FrancisUsher/fauxrmie/40s-2040rmie.kicad_sch

## KiCad design 40s-2040rmie.kicad_sch (2023-11-17)

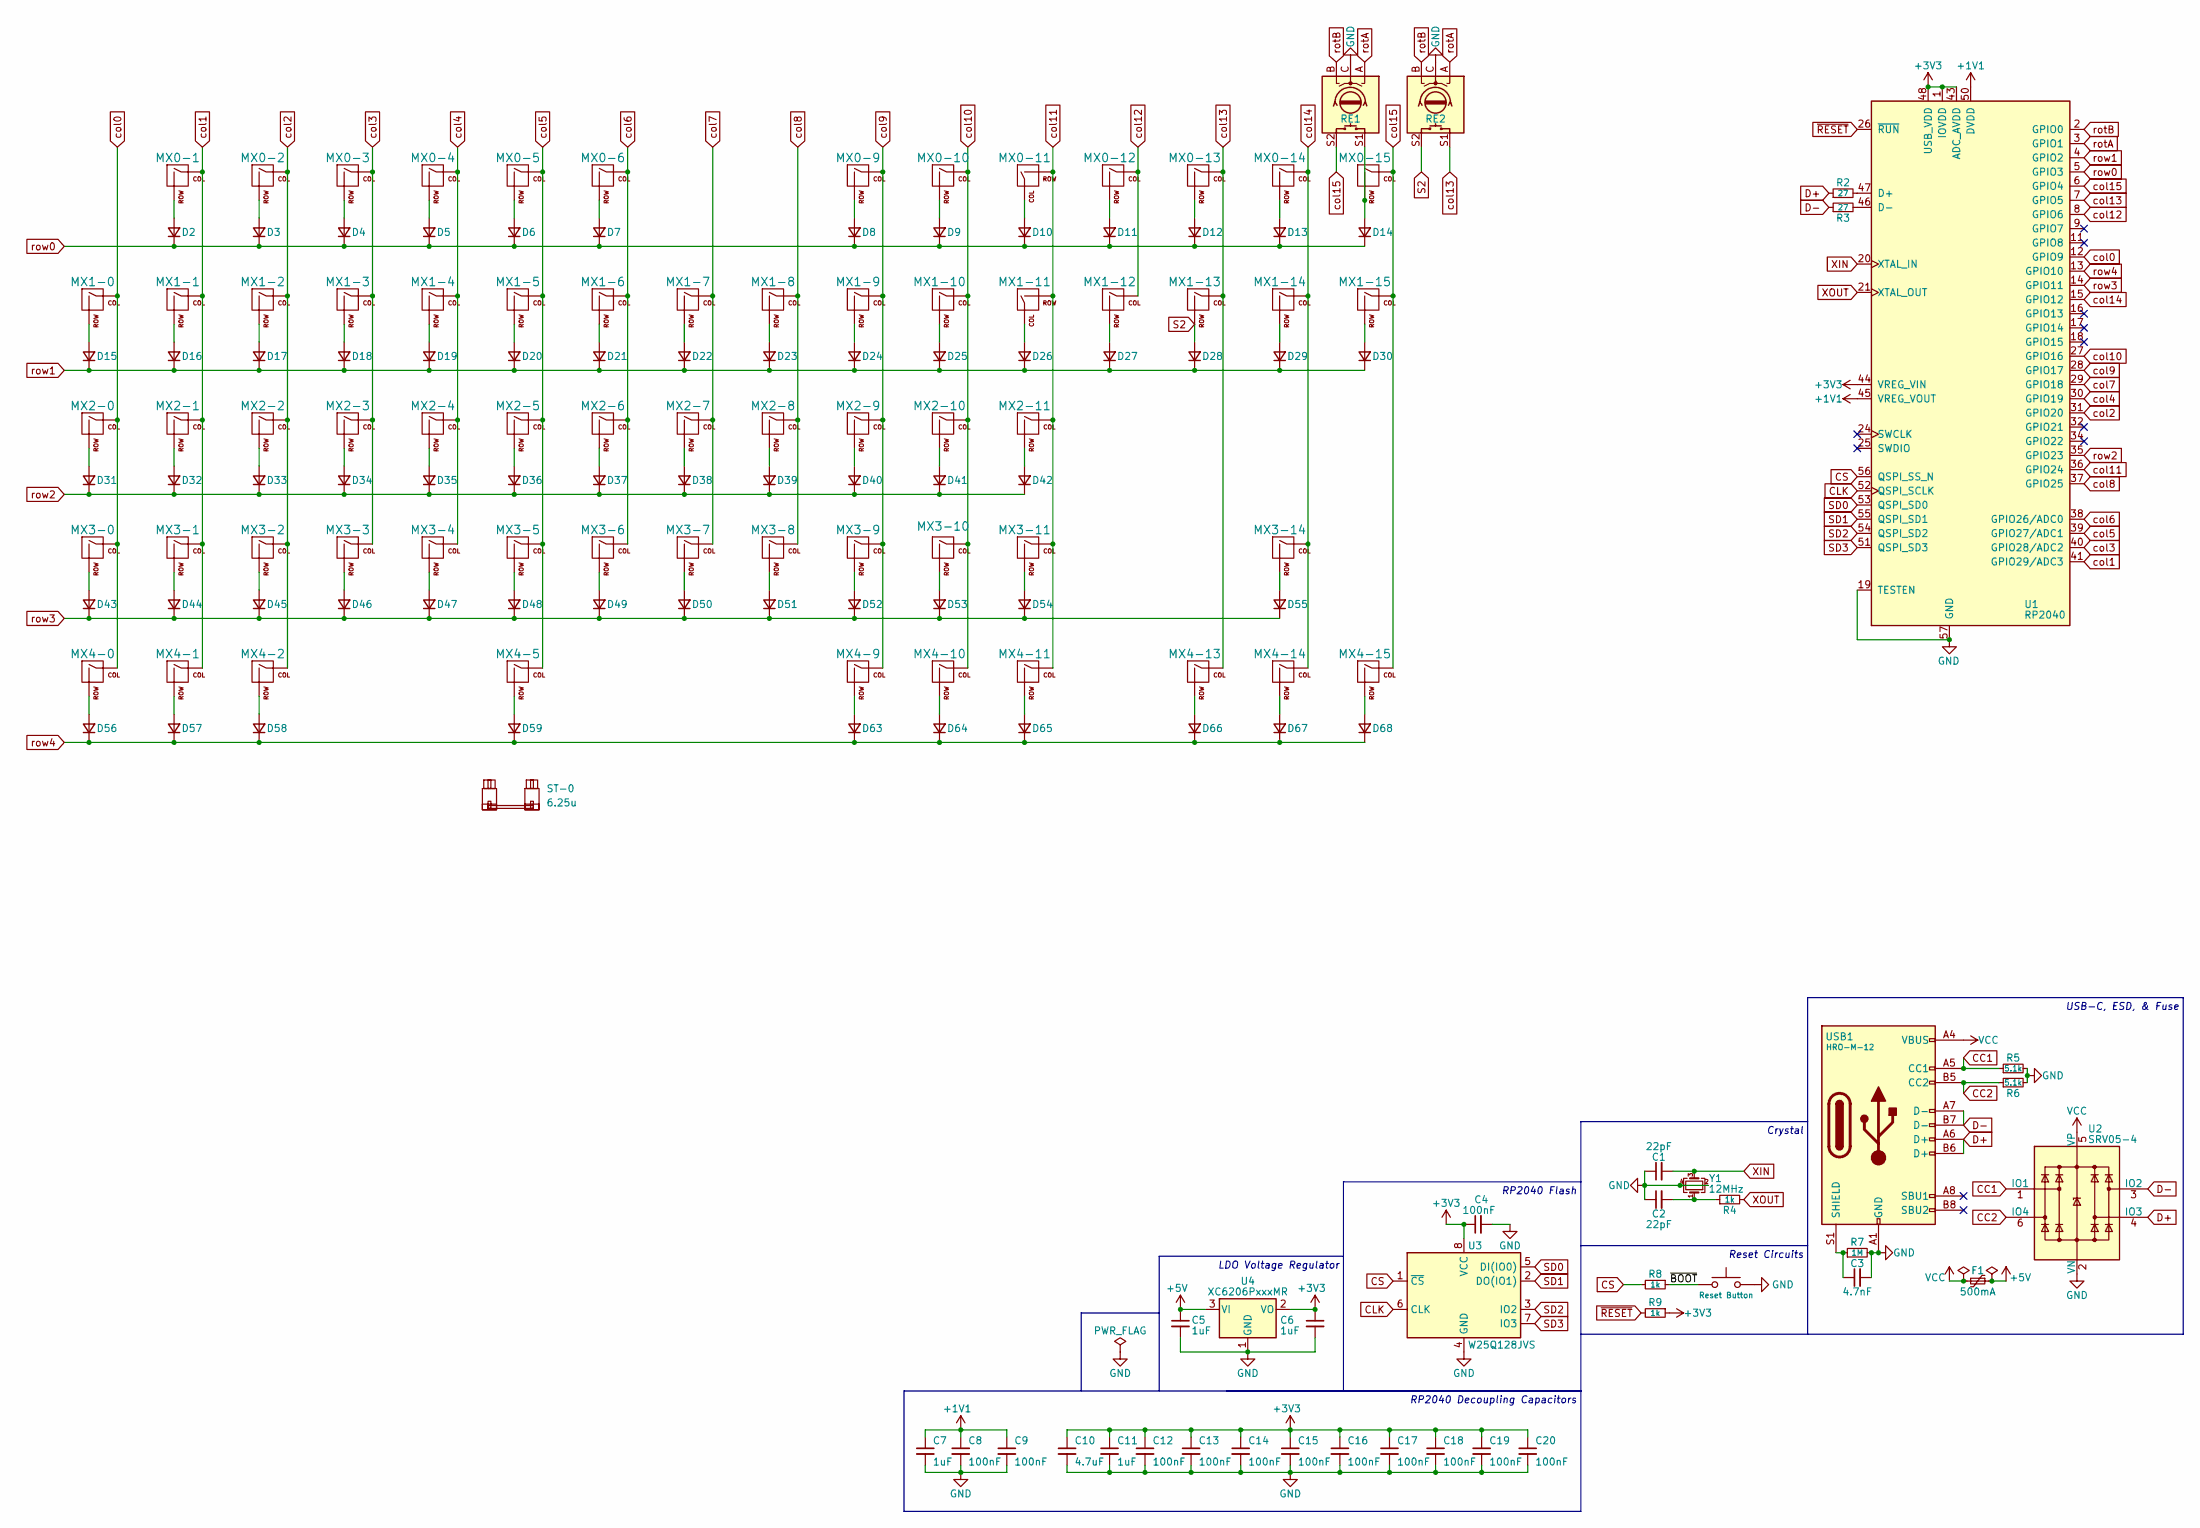
[picture p3: schematic 40s-2040rmie.kicad_sch]

Parts:
C1, C2: 22pF; C_0402_1005Metric
C3: 4.7nF; C_0402_1005Metric
C4, C8, C9, C12, C13, C14, C15, C16, C17, C18, C19, C20: 100nF; C_0402_1005Metric
C5, C6, C7, C11: 1uF; C_0402_1005Metric
C10: 4.7uF; C_0402_1005Metric
D2, D3, D4, D5, D6, D7, D8, D9, D10, D11, D12, D13, D14, D15, D16, D17, D18, D19, D20, D21, D22, D23, D24, D25, D26, D27, D28, D29, D30, D31, D32, D33, D34, D35, D36, D37, D38, D39, D40, D41, D42, D43, D44, D45, D46, D47, D48, D49, D50, D51, D52, D53, D54, D55, D56, D57, D58, D59, D63, D64, D65, D66, D67, D68: D_Small; D_SOD-123
F1: 500mA; Fuse_1206_3216Metric
MX0-1, MX0-2, MX0-3, MX0-4, MX0-5, MX0-6, MX0-9, MX0-10, MX0-11, MX0-12, MX0-13, MX0-14, MX0-15, MX1-0, MX1-1, MX1-2, MX1-3, MX1-4, MX1-5, MX1-6, MX1-7, MX1-8, MX1-9, MX1-10, MX1-11, MX1-12, MX1-13, MX1-14, MX1-15, MX2-1, MX2-2, MX2-3, MX2-4, MX2-5, MX2-6, MX2-7, MX2-8, MX2-9, MX2-10, MX3-1, MX3-2, MX3-3, MX3-4, MX3-5, MX3-6, MX3-7, MX3-8, MX3-9, MX3-10, MX3-14, MX4-5, MX4-9, MX4-10, MX4-11, MX4-13, MX4-14, MX4-15: MX-NoLED; SW_MX_1u
MX2-0, MX3-11, MX4-0, MX4-1, MX4-2: MX-NoLED; SW_MX_1.25u
MX2-11, MX3-0: MX-NoLED; SW_MX_1.75u
R2, R3: 27; R_0603_1608Metric
R4, R8, R9: 1k; R_0402_1005Metric
R5, R6: 5.1k; R_0402_1005Metric
R7: 1M; R_0402_1005Metric
RE1, RE2: RotaryEncoder_Switch; RotaryEncoder_Alps_EC11E-Switch_Vertical_H20mm
Reset1: Reset Button; SW_SPST_SKQG_WithStem
ST-0: 6.25u; STAB_MX_6.25u
U1: RP2040; RP2040-QFN-56
U2: SRV05-4; SOT-23-6-routable
U3: W25Q128JVS; SOIC-8_5.23x5.23mm_P1.27mm
U4: XC6206PxxxMR; SOT-23
USB1: HRO-M-12; USB_C_Receptacle_HRO_TYPE-C-31-M-12
Y1: 12MHz; Crystal_SMD_3225-4Pin_3.2x2.5mm

Connections:
+1V1: C7.1, C8.1, C9.1, U1.23 (DVDD), U1.45 (VREG_VOUT), U1.50 (DVDD)
+3V3: C4.1, C6.1, C10.1, C11.1, C12.1, C13.1, C14.1, C15.1, C16.1, C17.1, C18.1, C19.1, C20.1, R9.1, U1.1 (IOVDD), U1.10 (IOVDD), U1.22 (IOVDD), U1.33 (IOVDD), U1.42 (IOVDD), U1.43 (ADC_AVDD), U1.44 (VREG_VIN), U1.48 (USB_VDD), U1.49 (IOVDD), U3.8 (VCC), U4.2 (VO)
+5V: C5.1, F1.1, U4.3 (VI)
CC1: R5.1, U2.1 (IO1), USB1.A5 (CC1)
CC2: R6.1, U2.6 (IO4), USB1.B5 (CC2)
CLK: U1.52 (QSPI_SCLK), U3.6 (CLK)
CS: R8.2, U1.56 (QSPI_SS_N), U3.1 (~CS)
D+: R2.1, U2.4 (IO3), USB1.A6 (D+), USB1.B6 (D+)
D-: R3.1, U2.3 (IO2), USB1.A7 (D-), USB1.B7 (D-)
GND: C1.1, C2.1, C3.2, C4.2, C5.2, C6.2, C7.2, C8.2, C9.2, C10.2, C11.2, C12.2, C13.2, C14.2, C15.2, C16.2, C17.2, C18.2, C19.2, C20.2, R5.2, R6.2, R7.2, RE1.C, RE2.C, Reset1.2, U1.19 (TESTEN), U1.57 (GND), U2.2 (VN), U3.4 (GND), U4.1 (GND), USB1.A1 (GND), USB1.A12 (GND), USB1.B1 (GND), USB1.B12 (GND), Y1.2, Y1.4
unnamed: C2.2, R4.1, Y1.1
unnamed: C3.1, R7.1, USB1.S1 (SHIELD)
unnamed: D2.2 (A), MX0-1.2 (ROW)
unnamed: D3.2 (A), MX0-2.2 (ROW)
unnamed: D4.2 (A), MX0-3.2 (ROW)
unnamed: D5.2 (A), MX0-4.2 (ROW)
unnamed: D6.2 (A), MX0-5.2 (ROW)
unnamed: D7.2 (A), MX0-6.2 (ROW)
unnamed: D8.2 (A), MX0-9.2 (ROW)
unnamed: D9.2 (A), MX0-10.2 (ROW)
unnamed: D10.2 (A), MX0-11.1 (COL)
unnamed: D11.2 (A), MX0-12.2 (ROW)
unnamed: D12.2 (A), MX0-13.2 (ROW)
unnamed: D13.2 (A), MX0-14.2 (ROW)
unnamed: D14.2 (A), MX0-15.2 (ROW), RE1.S1
unnamed: D15.2 (A), MX1-0.2 (ROW)
unnamed: D16.2 (A), MX1-1.2 (ROW)
unnamed: D17.2 (A), MX1-2.2 (ROW)
unnamed: D18.2 (A), MX1-3.2 (ROW)
unnamed: D19.2 (A), MX1-4.2 (ROW)
unnamed: D20.2 (A), MX1-5.2 (ROW)
unnamed: D21.2 (A), MX1-6.2 (ROW)
unnamed: D22.2 (A), MX1-7.2 (ROW)
unnamed: D23.2 (A), MX1-8.2 (ROW)
unnamed: D24.2 (A), MX1-9.2 (ROW)
unnamed: D25.2 (A), MX1-10.2 (ROW)
unnamed: D26.2 (A), MX1-11.1 (COL)
unnamed: D27.2 (A), MX1-12.2 (ROW)
unnamed: D29.2 (A), MX1-14.2 (ROW)
unnamed: D30.2 (A), MX1-15.2 (ROW)
unnamed: D31.2 (A), MX2-0.2 (ROW)
unnamed: D32.2 (A), MX2-1.2 (ROW)
unnamed: D33.2 (A), MX2-2.2 (ROW)
unnamed: D34.2 (A), MX2-3.2 (ROW)
unnamed: D35.2 (A), MX2-4.2 (ROW)
unnamed: D36.2 (A), MX2-5.2 (ROW)
unnamed: D37.2 (A), MX2-6.2 (ROW)
unnamed: D38.2 (A), MX2-7.2 (ROW)
unnamed: D39.2 (A), MX2-8.2 (ROW)
unnamed: D40.2 (A), MX2-9.2 (ROW)
unnamed: D41.2 (A), MX2-10.2 (ROW)
unnamed: D42.2 (A), MX2-11.2 (ROW)
unnamed: D43.2 (A), MX3-0.2 (ROW)
unnamed: D44.2 (A), MX3-1.2 (ROW)
unnamed: D45.2 (A), MX3-2.2 (ROW)
unnamed: D46.2 (A), MX3-3.2 (ROW)
unnamed: D47.2 (A), MX3-4.2 (ROW)
unnamed: D48.2 (A), MX3-5.2 (ROW)
unnamed: D49.2 (A), MX3-6.2 (ROW)
unnamed: D50.2 (A), MX3-7.2 (ROW)
unnamed: D51.2 (A), MX3-8.2 (ROW)
unnamed: D52.2 (A), MX3-9.2 (ROW)
unnamed: D53.2 (A), MX3-10.2 (ROW)
unnamed: D54.2 (A), MX3-11.2 (ROW)
unnamed: D55.2 (A), MX3-14.2 (ROW)
unnamed: D56.2 (A), MX4-0.2 (ROW)
unnamed: D57.2 (A), MX4-1.2 (ROW)
unnamed: D58.2 (A), MX4-2.2 (ROW)
unnamed: D59.2 (A), MX4-5.2 (ROW)
unnamed: D63.2 (A), MX4-9.2 (ROW)
unnamed: D64.2 (A), MX4-10.2 (ROW)
unnamed: D65.2 (A), MX4-11.2 (ROW)
unnamed: D66.2 (A), MX4-13.2 (ROW)
unnamed: D67.2 (A), MX4-14.2 (ROW)
unnamed: D68.2 (A), MX4-15.2 (ROW)
unnamed: R2.2, U1.47 (D+)
unnamed: R3.2, U1.46 (D-)
S2: D28.2 (A), MX1-13.2 (ROW), RE2.S2
SD0: U1.53 (QSPI_SD0), U3.5 (DI(IO0))
SD1: U1.55 (QSPI_SD1), U3.2 (DO(IO1))
SD2: U1.54 (QSPI_SD2), U3.3 (IO2)
SD3: U1.51 (QSPI_SD3), U3.7 (IO3)
VCC: F1.2, U2.5 (VP), USB1.A4 (VBUS), USB1.A9 (VBUS), USB1.B4 (VBUS), USB1.B9 (VBUS)
XIN: C1.2, U1.20 (XTAL_IN), Y1.3
XOUT: R4.2, U1.21 (XTAL_OUT)
col0: MX1-0.1 (COL), MX2-0.1 (COL), MX3-0.1 (COL), MX4-0.1 (COL), U1.12 (GPIO9)
col1: MX0-1.1 (COL), MX1-1.1 (COL), MX2-1.1 (COL), MX3-1.1 (COL), MX4-1.1 (COL), U1.41 (GPIO29/ADC3)
col2: MX0-2.1 (COL), MX1-2.1 (COL), MX2-2.1 (COL), MX3-2.1 (COL), MX4-2.1 (COL), U1.31 (GPIO20)
col3: MX0-3.1 (COL), MX1-3.1 (COL), MX2-3.1 (COL), MX3-3.1 (COL), U1.40 (GPIO28/ADC2)
col4: MX0-4.1 (COL), MX1-4.1 (COL), MX2-4.1 (COL), MX3-4.1 (COL), U1.30 (GPIO19)
col5: MX0-5.1 (COL), MX1-5.1 (COL), MX2-5.1 (COL), MX3-5.1 (COL), MX4-5.1 (COL), U1.39 (GPIO27/ADC1)
col6: MX0-6.1 (COL), MX1-6.1 (COL), MX2-6.1 (COL), MX3-6.1 (COL), U1.38 (GPIO26/ADC0)
col7: MX1-7.1 (COL), MX2-7.1 (COL), MX3-7.1 (COL), U1.29 (GPIO18)
col8: MX1-8.1 (COL), MX2-8.1 (COL), MX3-8.1 (COL), U1.37 (GPIO25)
col9: MX0-9.1 (COL), MX1-9.1 (COL), MX2-9.1 (COL), MX3-9.1 (COL), MX4-9.1 (COL), U1.28 (GPIO17)
col10: MX0-10.1 (COL), MX1-10.1 (COL), MX2-10.1 (COL), MX3-10.1 (COL), MX4-10.1 (COL), U1.27 (GPIO16)
col11: MX0-11.2 (ROW), MX1-11.2 (ROW), MX2-11.1 (COL), MX3-11.1 (COL), MX4-11.1 (COL), U1.36 (GPIO24)
col12: MX0-12.1 (COL), MX1-12.1 (COL), U1.8 (GPIO6)
col13: MX0-13.1 (COL), MX1-13.1 (COL), MX4-13.1 (COL), RE2.S1, U1.7 (GPIO5)
col14: MX0-14.1 (COL), MX1-14.1 (COL), MX3-14.1 (COL), MX4-14.1 (COL), U1.15 (GPIO12)
col15: MX0-15.1 (COL), MX1-15.1 (COL), MX4-15.1 (COL), RE1.S2, U1.6 (GPIO4)
rotA: RE1.A, RE2.A, U1.3 (GPIO1)
rotB: RE1.B, RE2.B, U1.2 (GPIO0)
row0: D2.1 (K), D3.1 (K), D4.1 (K), D5.1 (K), D6.1 (K), D7.1 (K), D8.1 (K), D9.1 (K), D10.1 (K), D11.1 (K), D12.1 (K), D13.1 (K), D14.1 (K), U1.5 (GPIO3)
row1: D15.1 (K), D16.1 (K), D17.1 (K), D18.1 (K), D19.1 (K), D20.1 (K), D21.1 (K), D22.1 (K), D23.1 (K), D24.1 (K), D25.1 (K), D26.1 (K), D27.1 (K), D28.1 (K), D29.1 (K), D30.1 (K), U1.4 (GPIO2)
row2: D31.1 (K), D32.1 (K), D33.1 (K), D34.1 (K), D35.1 (K), D36.1 (K), D37.1 (K), D38.1 (K), D39.1 (K), D40.1 (K), D41.1 (K), D42.1 (K), U1.35 (GPIO23)
row3: D43.1 (K), D44.1 (K), D45.1 (K), D46.1 (K), D47.1 (K), D48.1 (K), D49.1 (K), D50.1 (K), D51.1 (K), D52.1 (K), D53.1 (K), D54.1 (K), D55.1 (K), U1.14 (GPIO11)
row4: D56.1 (K), D57.1 (K), D58.1 (K), D59.1 (K), D63.1 (K), D64.1 (K), D65.1 (K), D66.1 (K), D67.1 (K), D68.1 (K), U1.13 (GPIO10)
~BOOT: R8.1, Reset1.1
~RESET: R9.2, U1.26 (~RUN)

Notes on the sheet:
LDO Voltage Regulator
RP2040 Decoupling Capacitors
Crystal
RP2040 Flash
USB-C, ESD, & Fuse
Reset Circuits
